simonyiszk/sem-ultrahang/docs/img/H-bridge-and-driver.png

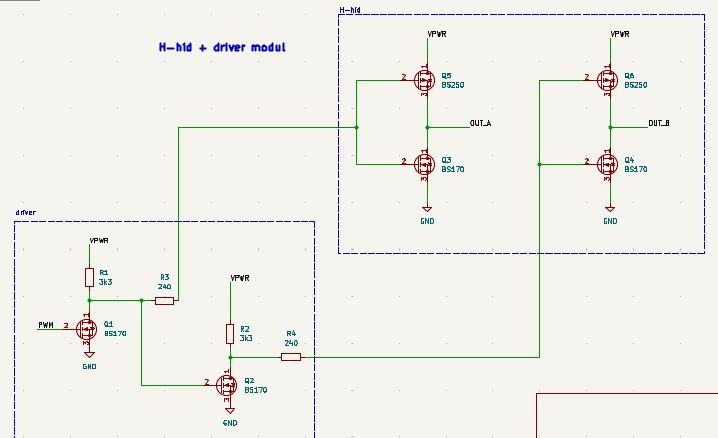
docs/img/H-bridge-and-driver.png
