simonyiszk/sem-ultrahang/simulation/555_psu/555_boost2.asc

C1: cap; 100µ
C2: cap; 10n
D1: diode; 1N4148
I2: current; 80m
L: ind; 220µ
Q1: npn; 2N3904
Q2: npn; 2N3904
R1: res; 1k
R2: res; 1k
R3: res; 6k
R4: res; 240
R5: res; 1k
U1: NE555
V1: voltage; 5
Named nets: 0, Vcc, Vout, Usw, Vd, CV
.tran 1
10k poti
valójában semmit sem tudunk a diódáról a nyitófeszültségén kívül
