simonyiszk/sem-ultrahang/simulation/555_psu/555_boost.asc

C1: cap; 100µ
C2: cap; 100n
D1: diode; 1N4148
I1: current; PULSE(30m 100m 100m 1p 1p 100m 200m 5)
L: ind; 10m
Q1: npn; BC817-16
Q2: npn; BC817-16
R1: res; 3k3
R2: res; 330
R3: res; 9450
R4: res; 550
R5: res; 330
U1: NE555
V1: voltage; 5
Named nets: 0, Vcc, Vout, Usw, Vd
.tran 10
