simonyiszk/sem-ultrahang/40Mhzmodulator2/40Mhzmodulator2.kicad_sch

## KiCad design 40Mhzmodulator2/40Mhzmodulator2.kicad_sch (2025-05-22)

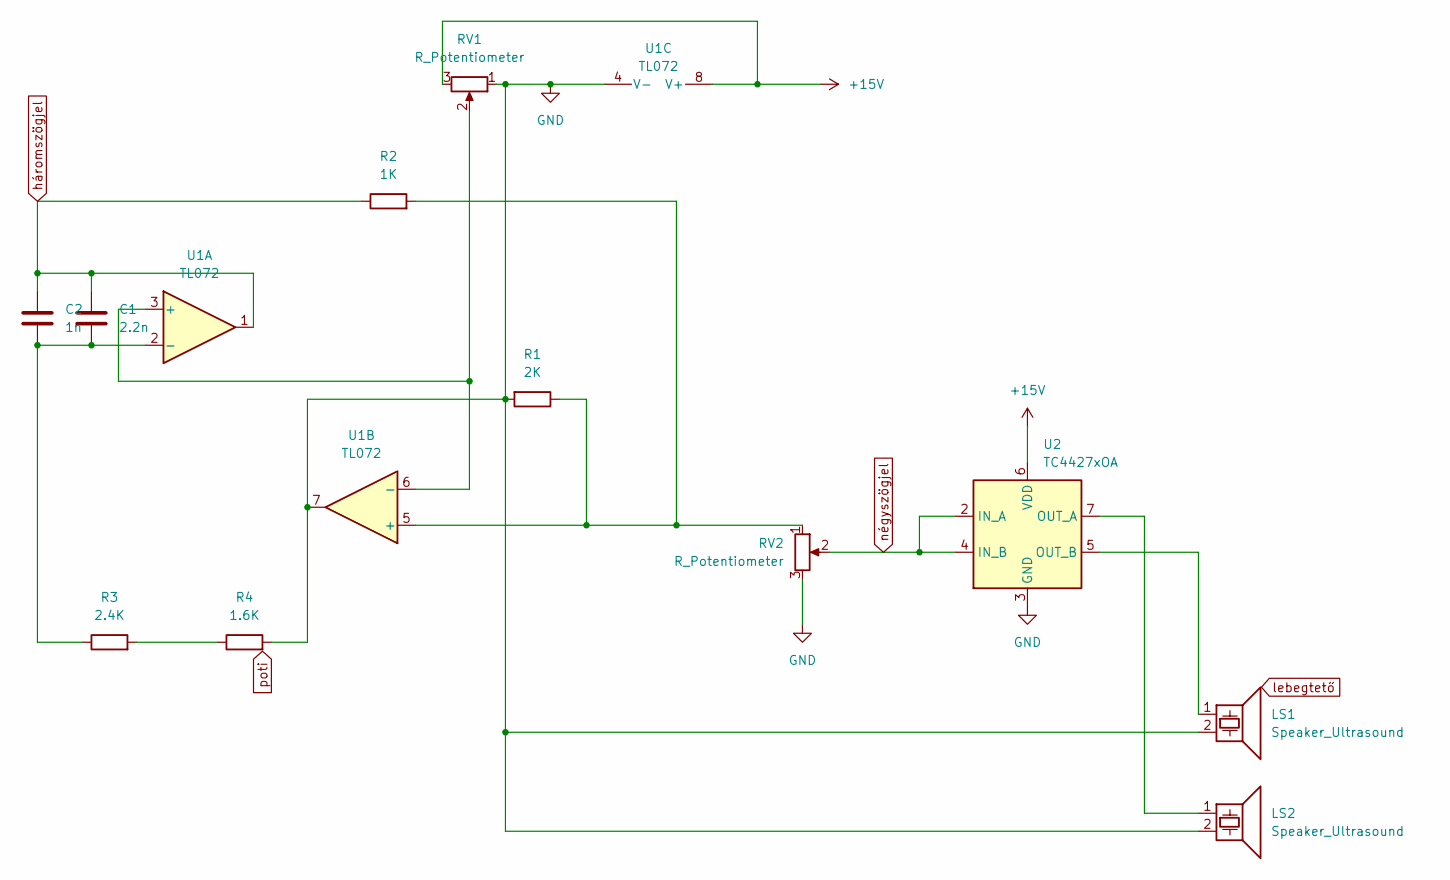
[picture p23: schematic 40Mhzmodulator2.kicad_sch]

Parts:
C1: 2.2n
C2: 1n
LS1, LS2: Speaker_Ultrasound
R1: 2K
R2: 1K
R3: 2.4K
R4: 1.6K
RV1, RV2: R_Potentiometer
U1: TL072
U2: TC4427xOA; SOIC-8_3.9x4.9mm_P1.27mm

Connections:
+15V: RV1.3, U1.8 (V+), U2.6 (VDD)
GND: LS1.2, LS2.2, R1.2, R4.2, RV1.1, RV2.3, U1.4 (V-), U1.7, U2.3 (GND)
unnamed: C1.2, C2.2, R3.1, U1.2 (-)
unnamed: LS1.1, U2.5 (OUT_B)
unnamed: LS2.1, U2.7 (OUT_A)
unnamed: R1.1, R2.2, RV2.1, U1.5 (+)
unnamed: R3.2, R4.1
unnamed: RV1.2, U1.3 (+), U1.6 (-)
háromszögjel: C1.1, C2.1, R2.1, U1.1
négyszögjel: RV2.2, U2.2 (IN_A), U2.4 (IN_B)
