simonyiszk/sem-ultrahang/lebegteto_analog/hbridge-drv.kicad_sch

## KiCad design lebegteto_analog/hbridge-drv.kicad_sch (2025-06-26)

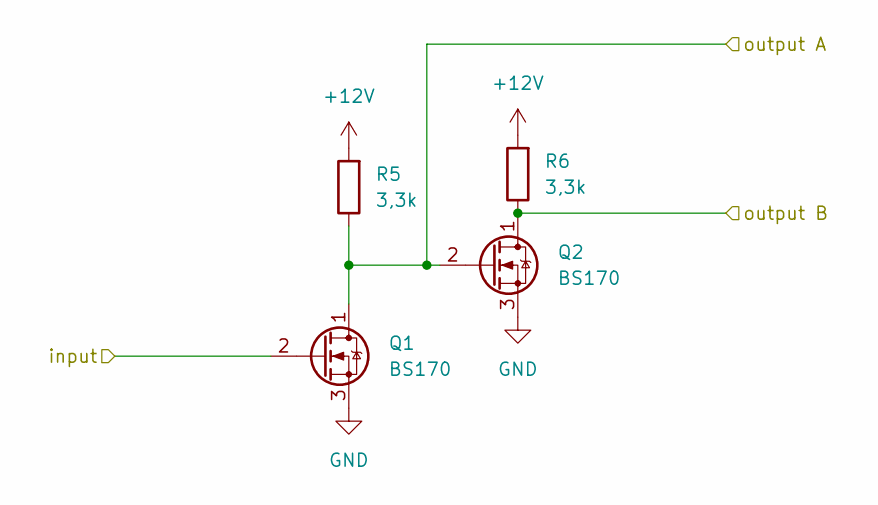
[picture p24: schematic hbridge-drv.kicad_sch]

Parts:
Q1, Q2: BS170; TO-92_Inline
R5, R6: 3,3k

Connections:
+12V: R5.2, R6.2
GND: Q1.3 (S), Q2.3 (S)
input: Q1.2 (G)
output A: Q1.1 (D), Q2.2 (G), R5.1
output B: Q2.1 (D), R6.1
