simonyiszk/sem-ultrahang/lebegteto_analog/hbridge.kicad_sch

## KiCad design lebegteto_analog/hbridge.kicad_sch (2025-06-26)

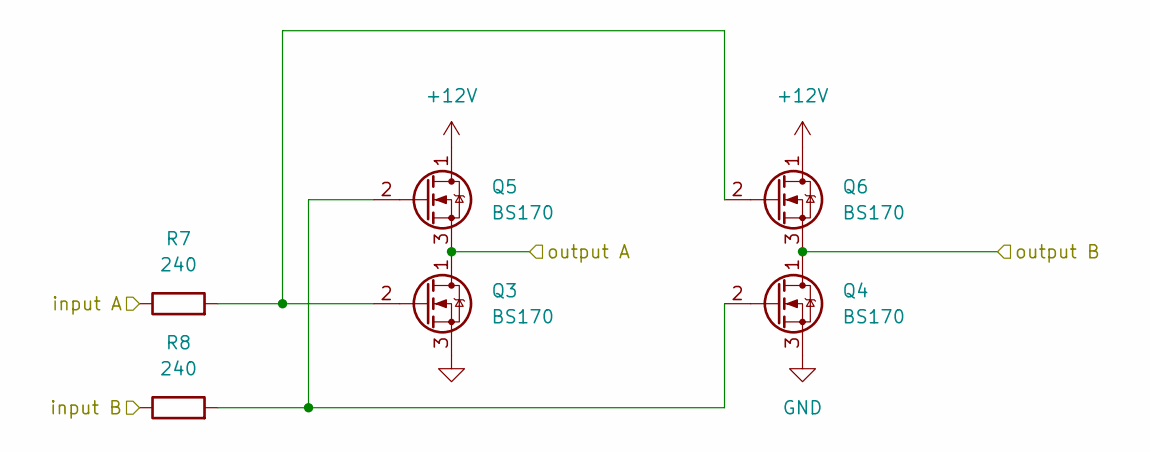
[picture p25: schematic hbridge.kicad_sch]

Parts:
Q3, Q4, Q5, Q6: BS170; TO-92_Inline
R7, R8: 240

Connections:
+12V: Q5.1 (D), Q6.1 (D)
GND: Q3.3 (S), Q4.3 (S)
unnamed: Q3.2 (G), Q6.2 (G), R7.2
unnamed: Q4.2 (G), Q5.2 (G), R8.2
input A: R7.1
input B: R8.1
output A: Q3.1 (D), Q5.3 (S)
output B: Q4.1 (D), Q6.3 (S)
