simonyiszk/sem-ultrahang/lebegteto_analog/jelgen.kicad_sch

## KiCad design lebegteto_analog/jelgen.kicad_sch (2025-06-26)

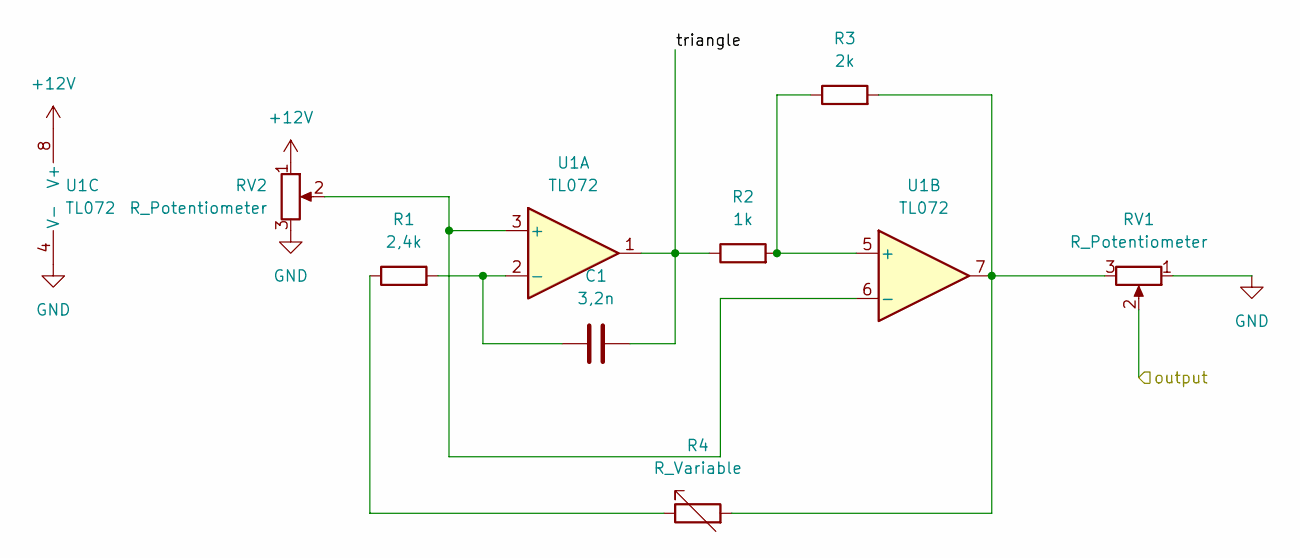
[picture p26: schematic jelgen.kicad_sch]

Parts:
C1: 3,2n
R1: 2,4k
R2: 1k
R3: 2k
R4: R_Variable
RV1, RV2: R_Potentiometer
U1: TL072

Connections:
+12V: RV2.1, U1.8 (V+)
GND: RV1.1, RV2.3, U1.4 (V-)
unnamed: C1.1, R1.2, U1.2 (-)
unnamed: R1.1, R4.1
unnamed: R2.2, R3.1, U1.5 (+)
unnamed: R3.2, R4.2, RV1.3, U1.7
unnamed: RV2.2, U1.3 (+), U1.6 (-)
output: RV1.2
triangle: C1.2, R2.1, U1.1
