simonyiszk/sem-ultrahang/lebegteto_analog/lebegteto_analog.kicad_sch

## KiCad design lebegteto_analog/lebegteto_analog.kicad_sch (2025-06-26)

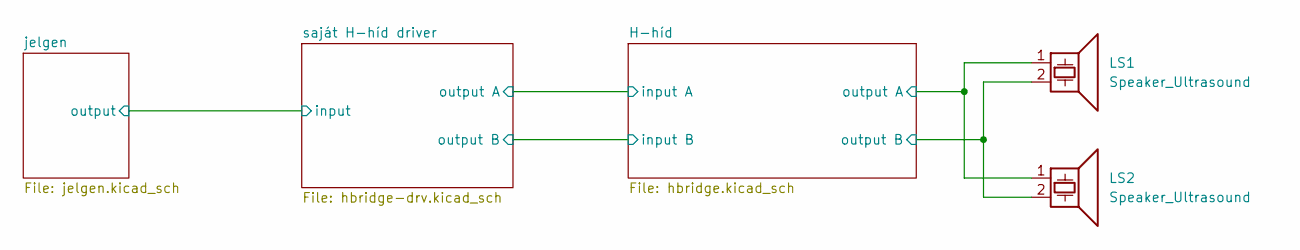
[picture p27: schematic lebegteto_analog.kicad_sch]

Parts:
LS1, LS2: Speaker_Ultrasound

Connections:
output A: LS1.1, LS2.1
output B: LS1.2, LS2.2
